weesing/smartglasses/design/049screen.3mf

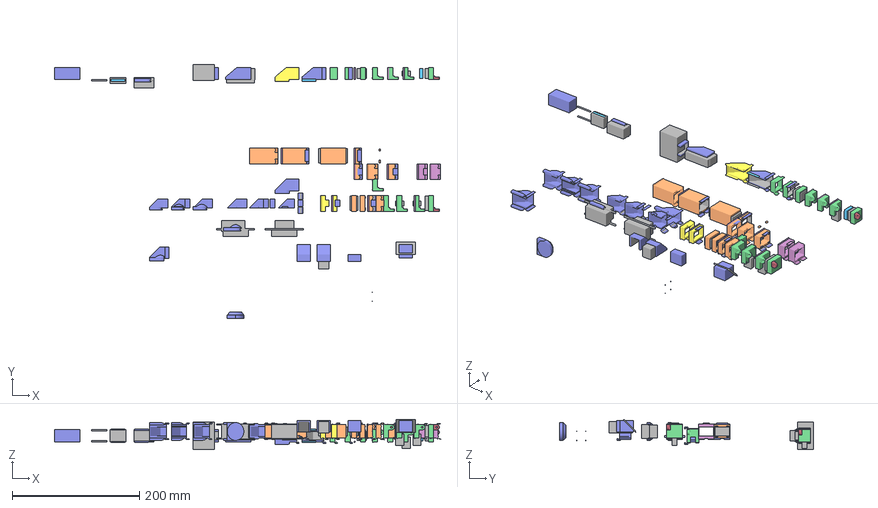
[picture p25: CAD file, 2021-08-19]
design/049screen.3mf
605.9 x 398.1 x 47.5 mm
