weesing/smartglasses/STLs/096screenrgb_housing.stl

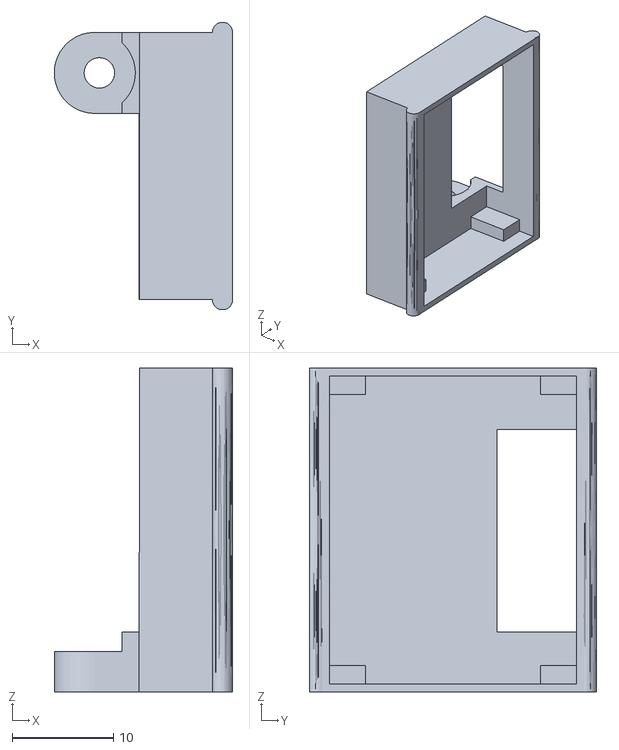
[picture p26: CAD file, 2021-08-24]
STLs/096screenrgb_housing.stl
17.6 x 28.4 x 32.0
