weesing/smartglasses/design/042screen.3mf

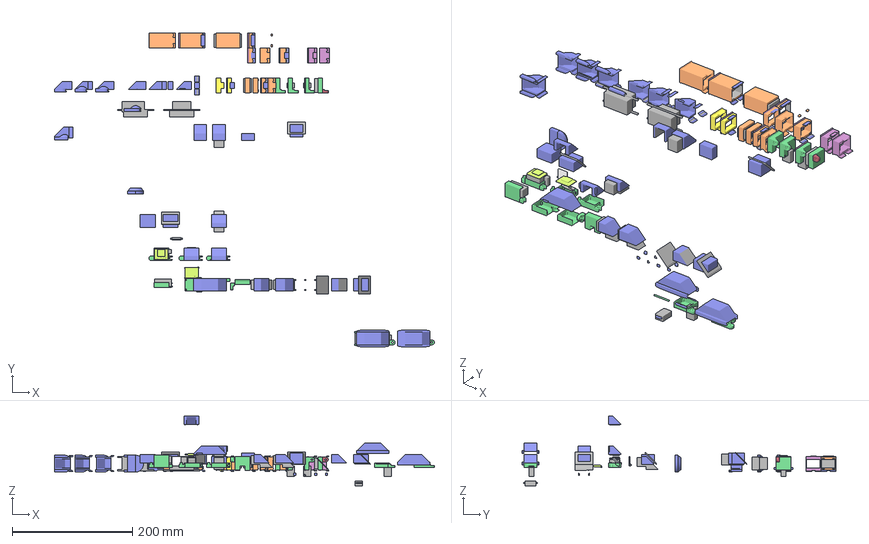
[picture p27: CAD file, 2021-08-19]
design/042screen.3mf
631.2 x 521.3 x 116.3 mm
