weesing/smartglasses/STLs/stem.stl

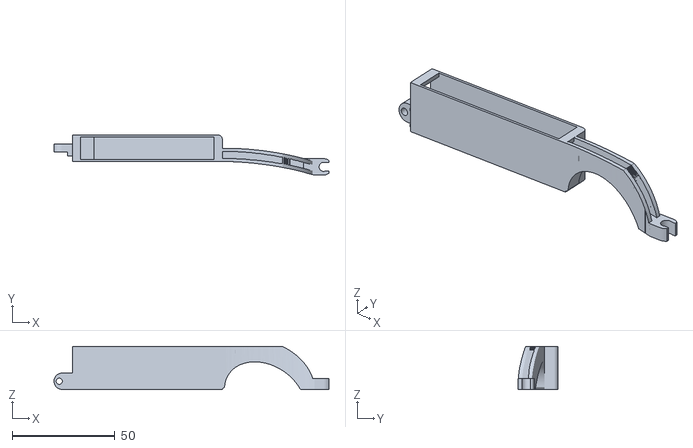
[picture p28: CAD file, 2021-08-21]
STLs/stem.stl
134.0 x 19.5 x 21.0
