weesing/smartglasses/design/096screen.3mf

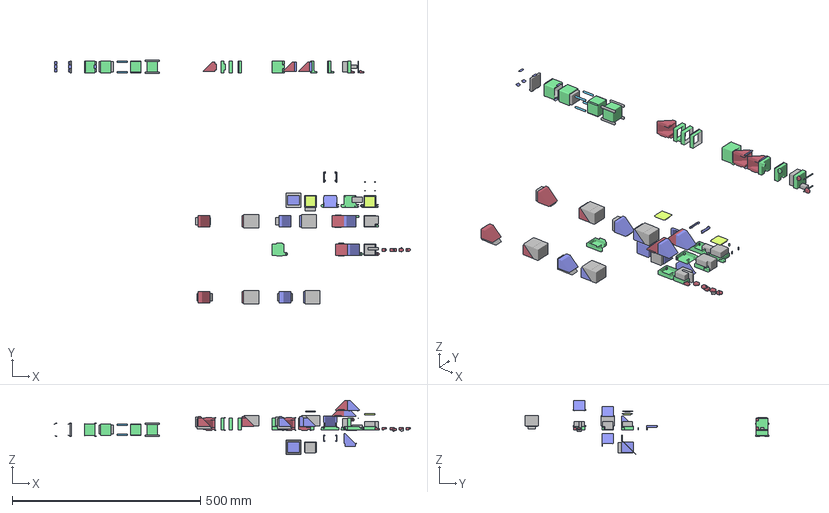
[picture p29: CAD file, 2021-08-19]
design/096screen.3mf
946.6 x 648.4 x 144.0 mm
