weesing/smartglasses/STLs/096screenrgb_mirror_housing.stl

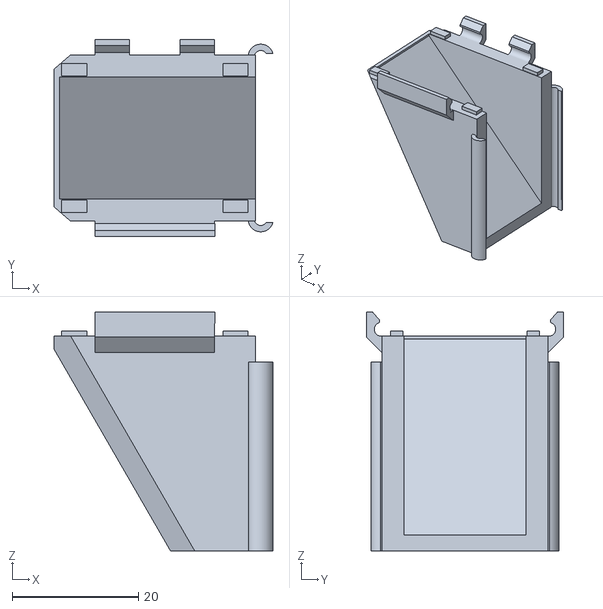
[picture p30: CAD file, 2021-08-21]
STLs/096screenrgb_mirror_housing.stl
34.7 x 31.3 x 37.9
