weesing/smartglasses/STLs/stem_cover.stl

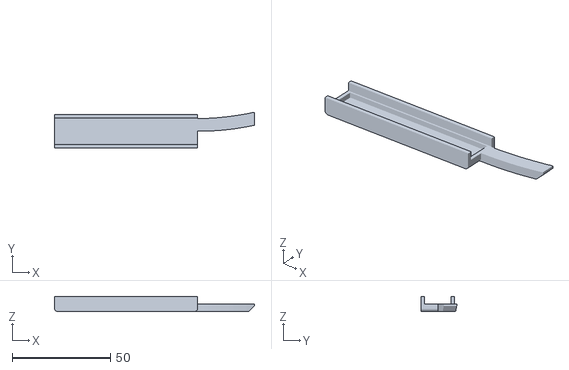
[picture p31: CAD file, 2021-08-21]
STLs/stem_cover.stl
102.0 x 18.2 x 7.60
