weesing/smartglasses/STLs/096screenrgb_lens_b.stl

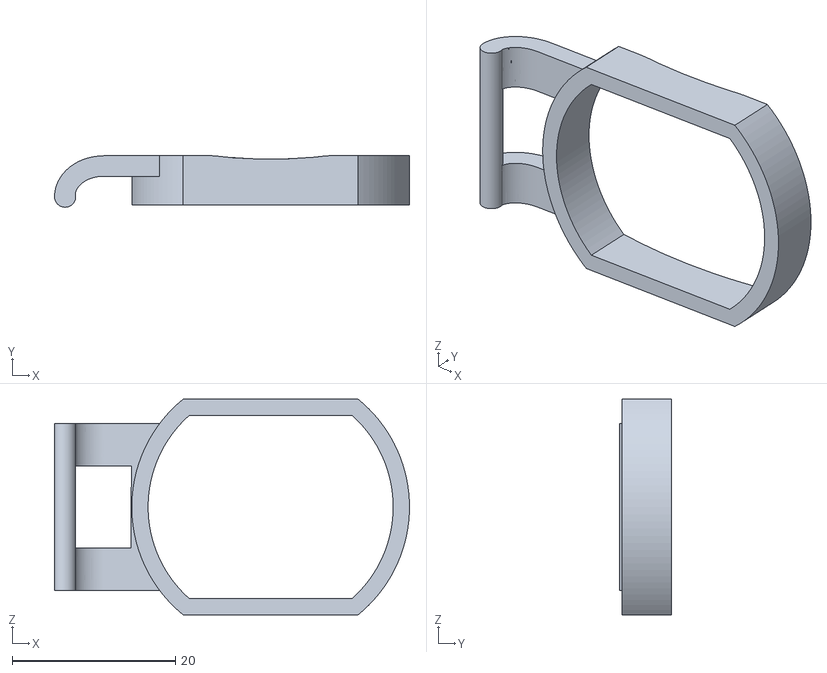
[picture p32: CAD file, 2021-08-21]
STLs/096screenrgb_lens_b.stl
43.5 x 6.31 x 26.4
