weesing/smartglasses/STLs/049mirror_housing.stl

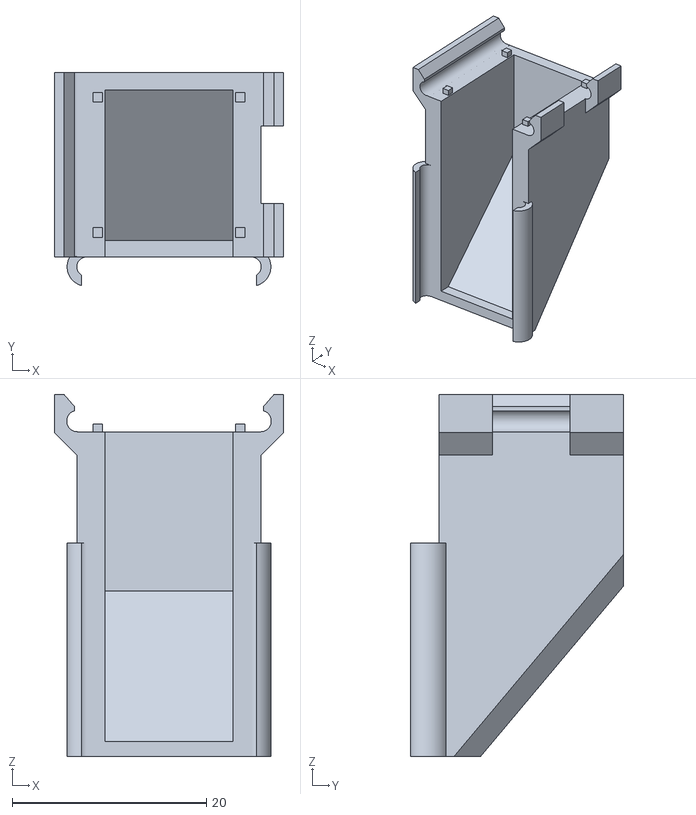
[picture p33: CAD file, 2021-08-19]
STLs/049mirror_housing.stl
23.6 x 22.0 x 37.3
