weesing/smartglasses/STLs/049lens_display_arm.stl

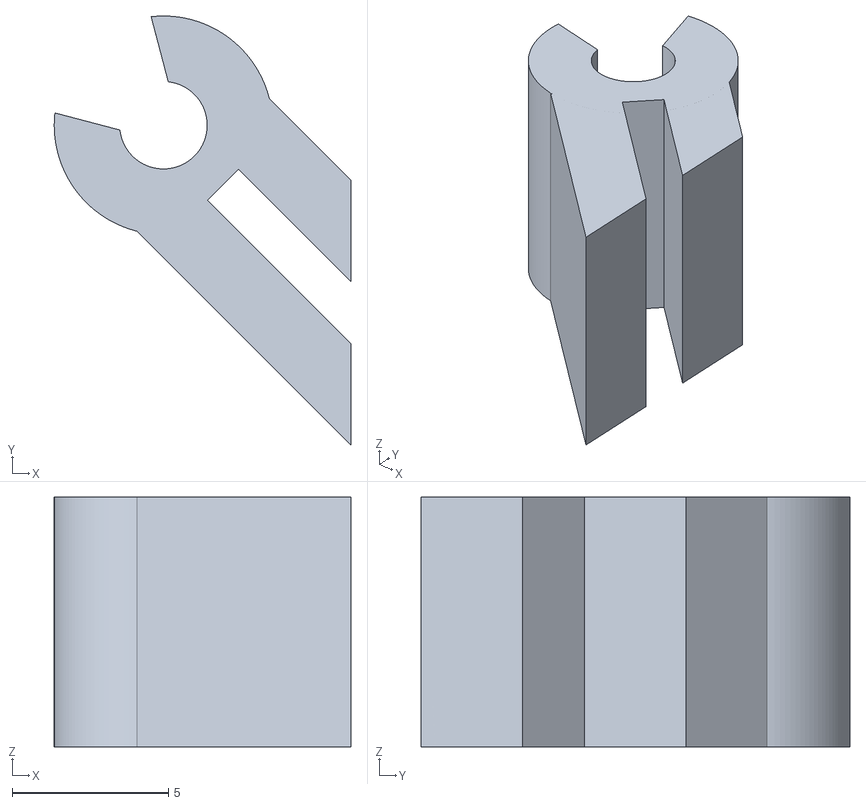
[picture p34: CAD file, 2021-08-19]
STLs/049lens_display_arm.stl
9.50 x 13.7 x 8.00
