weesing/smartglasses/STLs/battery.stl

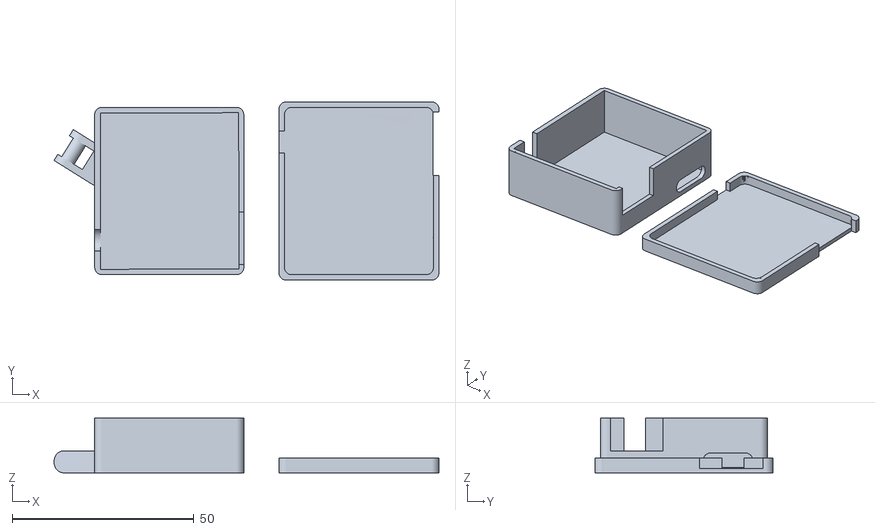
[picture p35: CAD file, 2021-08-19]
STLs/battery.stl
105.8 x 49.0 x 15.0
