weesing/smartglasses/STLs/049lens_a.stl

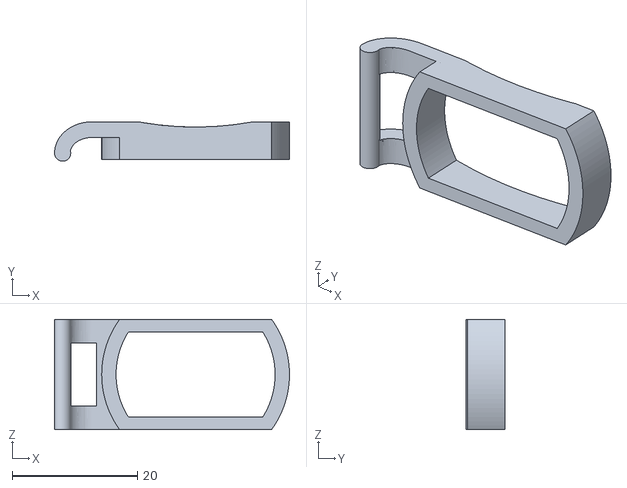
[picture p36: CAD file, 2021-08-19]
STLs/049lens_a.stl
37.5 x 6.31 x 17.6
