weesing/smartglasses/STLs/049screen_housing.stl

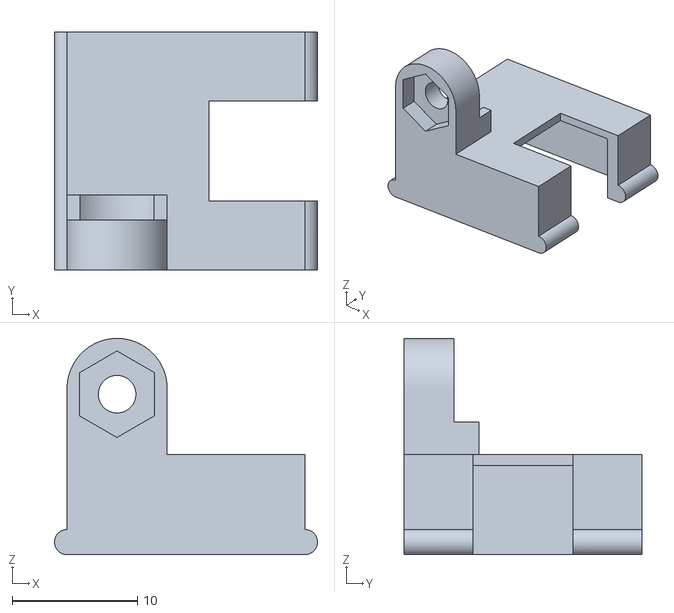
[picture p37: CAD file, 2021-08-19]
STLs/049screen_housing.stl
21.0 x 19.0 x 17.3
