weesing/smartglasses/STLs/049lens_b.stl

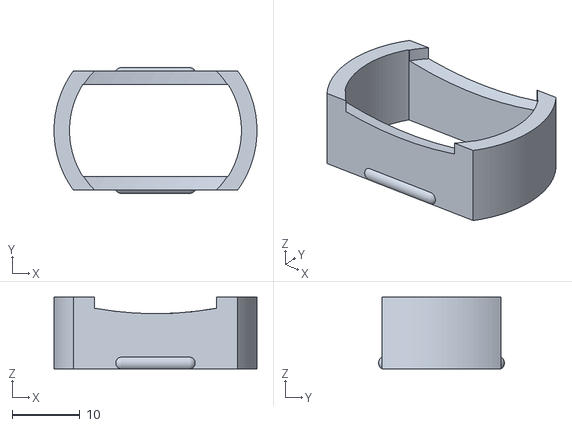
[picture p38: CAD file, 2021-08-19]
STLs/049lens_b.stl
30.0 x 18.6 x 10.6
