weesing/smartglasses/src/rpi/rpi_spi.h

/*
 * wiringPiSPI.h:
 *	Simplified SPI access routines
 *	Copyright (c) 2012-2015 Gordon Henderson
 ***********************************************************************
 * This file is part of wiringPi:
 *	https://projects.drogon.net/raspberry-pi/wiringpi/
 *
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
 *    You should have received a copy of the GNU Lesser General Public
 *    License along with wiringPi.
 *    If not, see <http://www.gnu.org/licenses/>.
 ***********************************************************************
 */

#ifdef __cplusplus
extern "C"
{
#endif

  int spi_write_16(int channel, uint16_t *data, int len);
  int spi_write(int channel, unsigned char *data, int len);
  int spi_init(int channel, int speed, int mode);

#ifdef __cplusplus
}
#endif
